WilFehr/puzzleroom/Solidworks/pcbmodel.SLDPRT

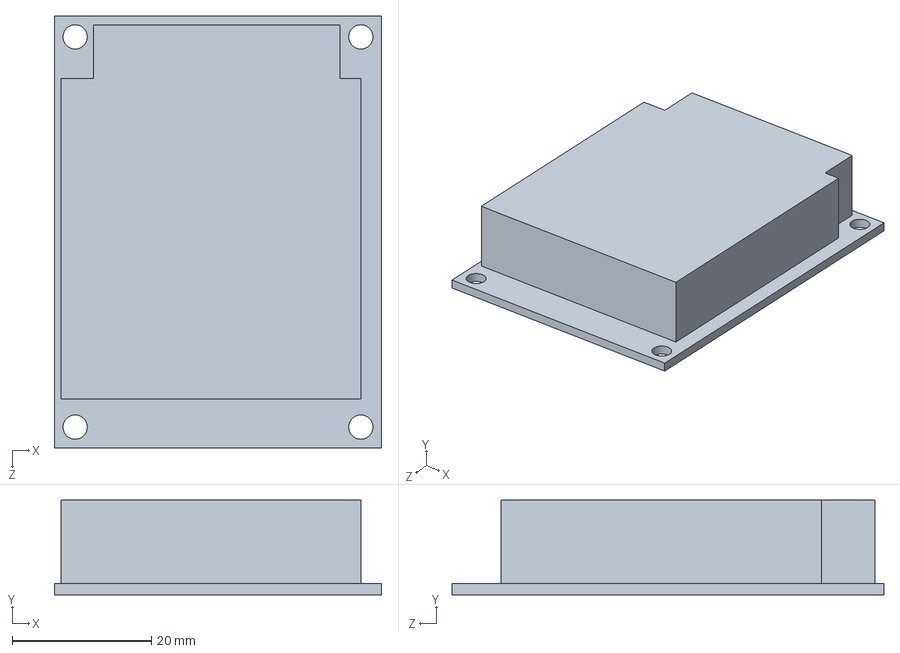
[picture p12: CAD file, 2025-03-24]
Solidworks/pcbmodel.SLDPRT
47.0 x 13.6 x 62.0 mm
